josefholmner/Holmner6Axis/3D-models/SolidWorksProject/Axis4_Holder.SLDPRT

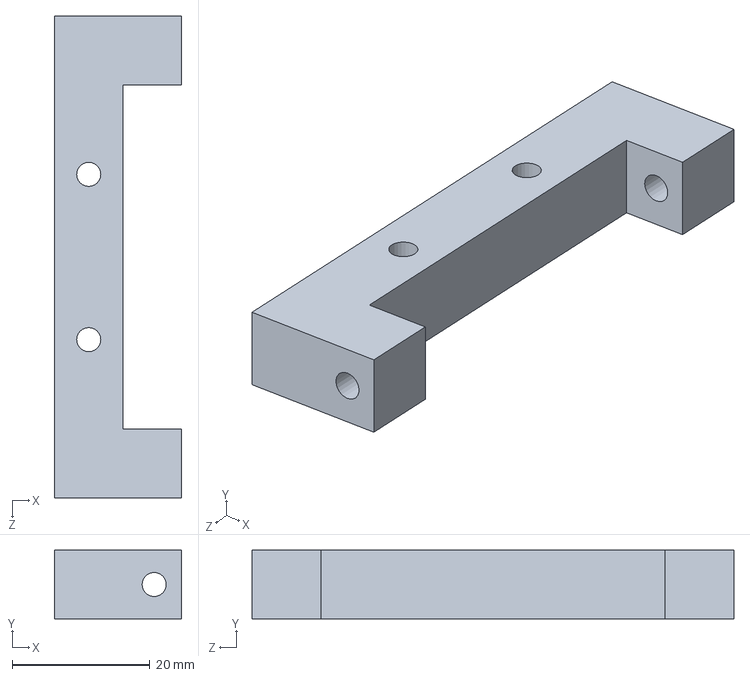
[picture p12: CAD file, 2020-04-25]
3D-models/SolidWorksProject/Axis4_Holder.SLDPRT
18.5 x 10.0 x 70.0 mm
