josefholmner/Holmner6Axis/3D-models/SolidWorksProject/Axis4_Rod.SLDPRT

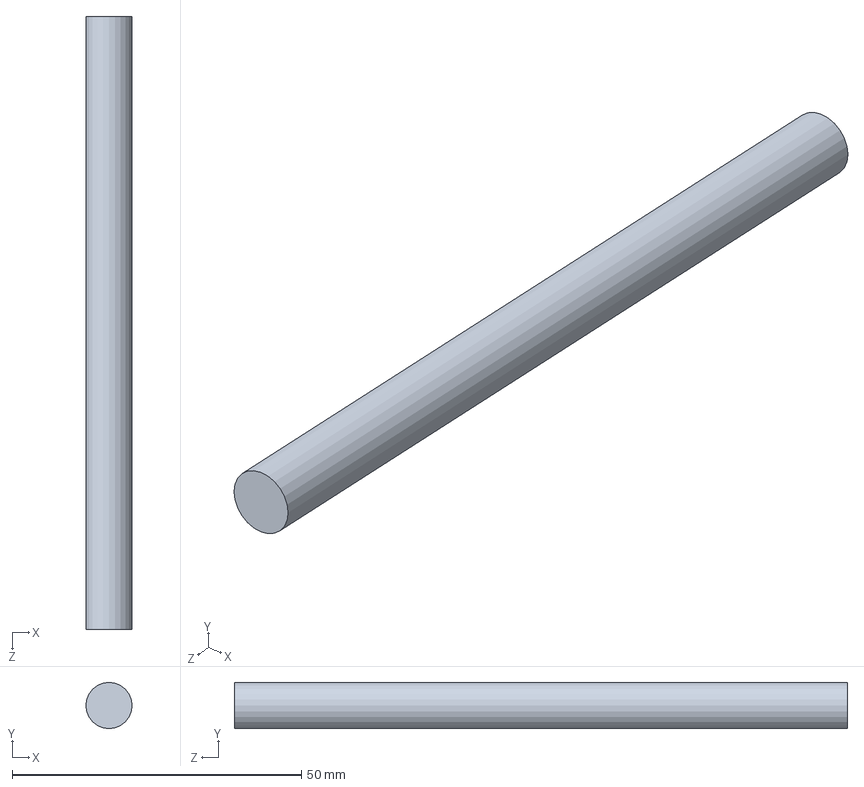
[picture p13: CAD file, 2020-04-25]
3D-models/SolidWorksProject/Axis4_Rod.SLDPRT
8.00 x 8.00 x 106.0 mm
