josefholmner/Holmner6Axis/3D-models/SolidWorksProject/Axis2_Arm_1.SLDPRT

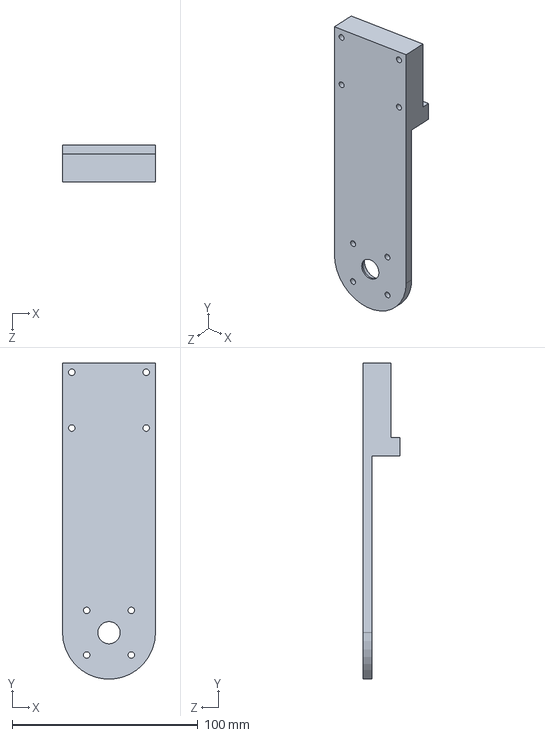
[picture p14: CAD file, 2020-04-25]
3D-models/SolidWorksProject/Axis2_Arm_1.SLDPRT
50.0 x 169.9 x 20.0 mm
