josefholmner/Holmner6Axis/3D-models/SolidWorksProject/Axis5_Cog.SLDPRT

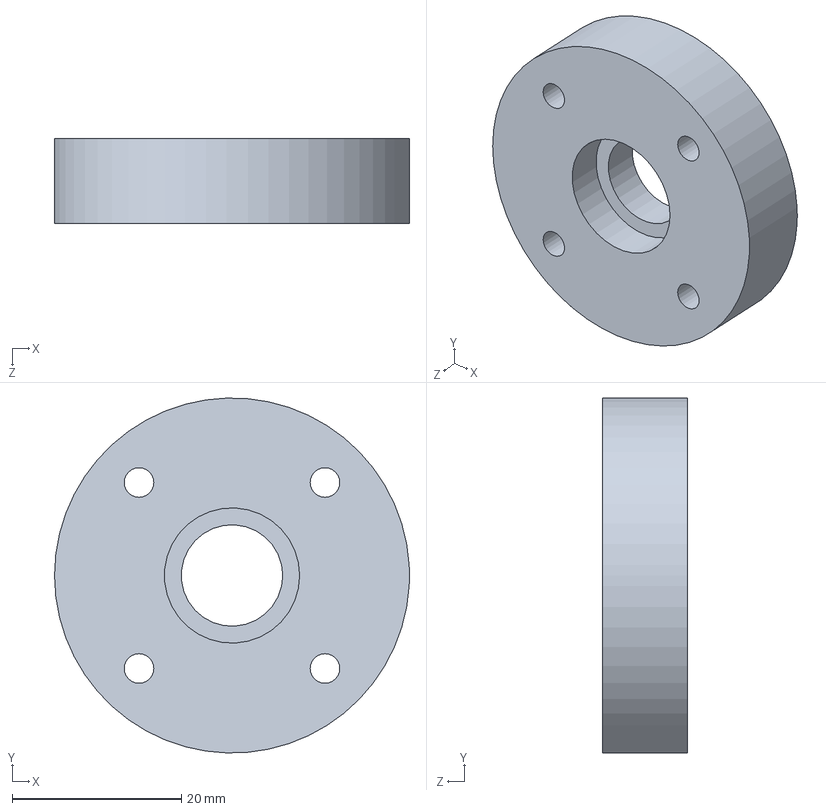
[picture p15: CAD file, 2020-04-25]
3D-models/SolidWorksProject/Axis5_Cog.SLDPRT
42.0 x 42.0 x 10.0 mm
