josefholmner/Holmner6Axis/3D-models/SolidWorksProject/Axis1_Cog.SLDPRT

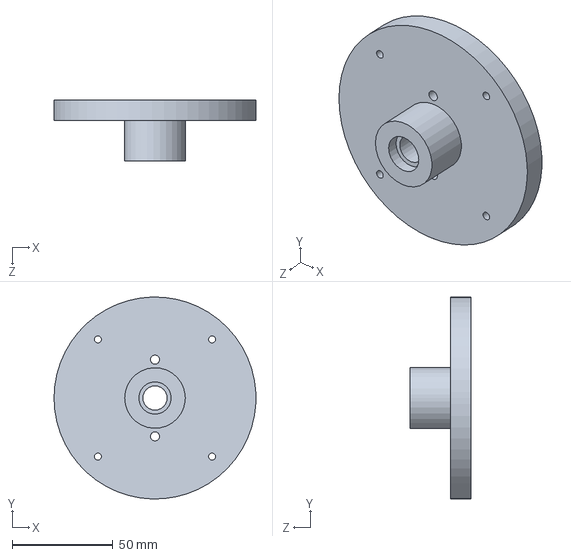
[picture p16: CAD file, 2020-04-25]
3D-models/SolidWorksProject/Axis1_Cog.SLDPRT
100.0 x 100.0 x 30.0 mm
