josefholmner/Holmner6Axis/3D-models/FreeCad/MotorCog_8mm.FCStd

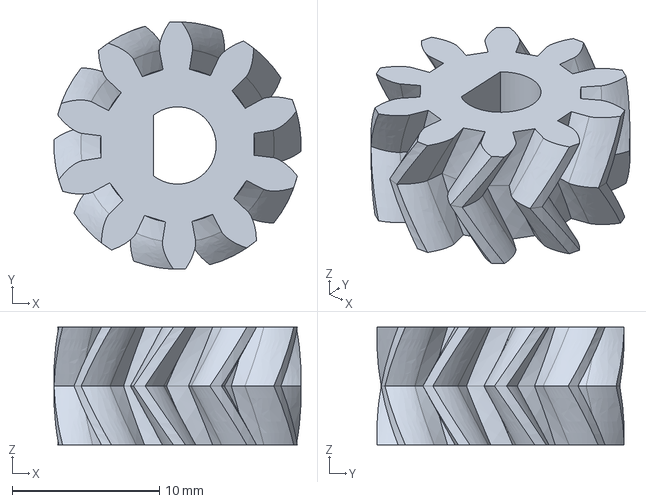
[picture p17: CAD file, 2026-01-18]
3D-models/FreeCad/MotorCog_8mm.FCStd
16.8 x 16.8 x 8.01 mm
