josefholmner/Holmner6Axis/3D-models/SolidWorksProject/Axis5_Rod.SLDPRT

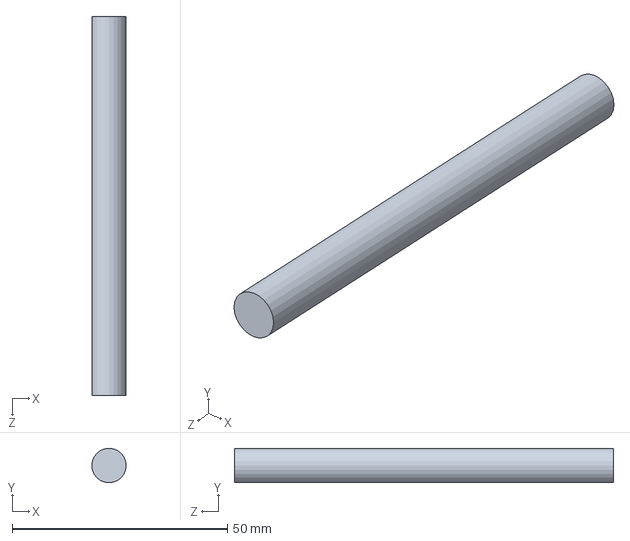
[picture p18: CAD file, 2020-04-25]
3D-models/SolidWorksProject/Axis5_Rod.SLDPRT
8.00 x 8.00 x 88.0 mm
