josefholmner/Holmner6Axis/3D-models/FreeCad/BasePlate.FCStd

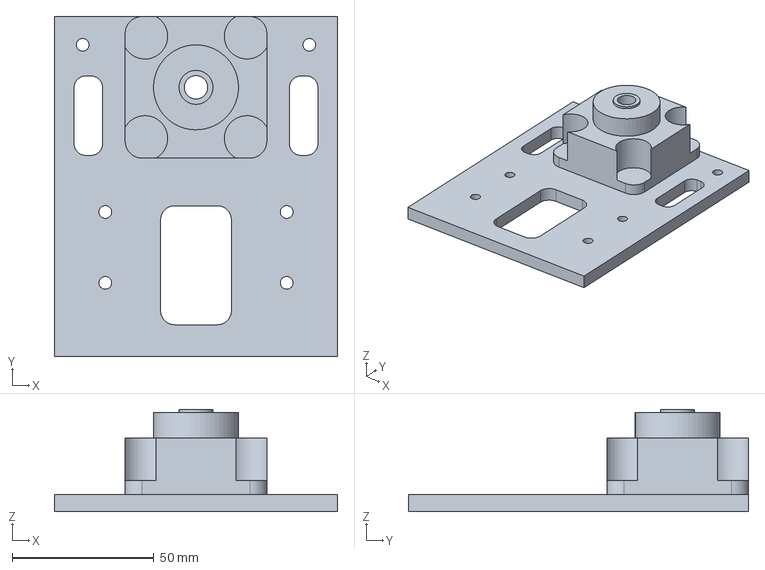
[picture p19: CAD file, 2026-01-17]
3D-models/FreeCad/BasePlate.FCStd
100.0 x 120.0 x 36.0 mm
