josefholmner/Holmner6Axis/3D-models/SolidWorksProject/Axis5_Arm_2_Left.SLDPRT

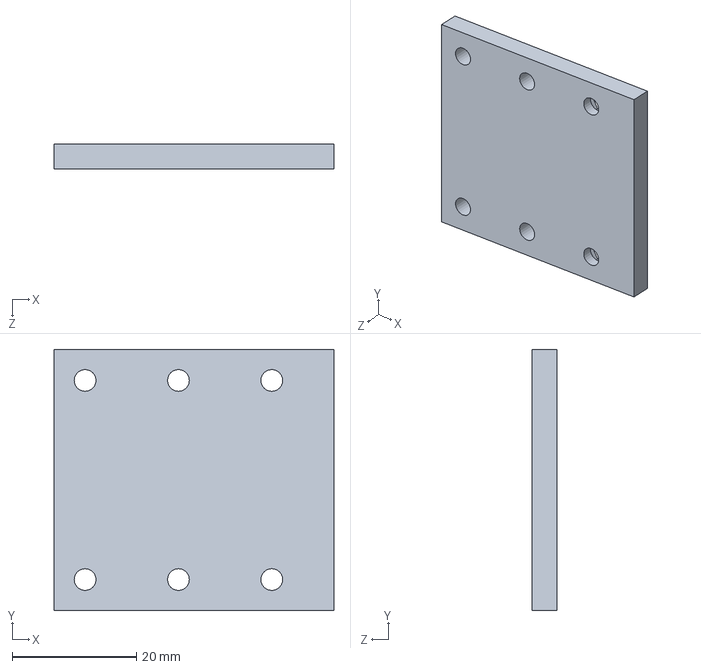
[picture p20: CAD file, 2020-04-25]
3D-models/SolidWorksProject/Axis5_Arm_2_Left.SLDPRT
45.0 x 42.0 x 4.00 mm
