josefholmner/Holmner6Axis/3D-models/SolidWorksProject/Axis2_Holder.SLDPRT

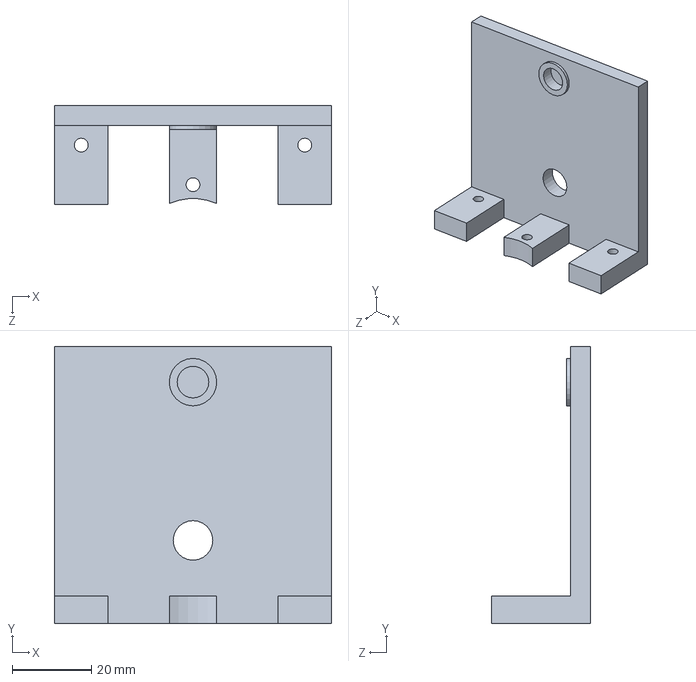
[picture p21: CAD file, 2020-04-25]
3D-models/SolidWorksProject/Axis2_Holder.SLDPRT
70.0 x 70.0 x 25.0 mm
