josefholmner/Holmner6Axis/3D-models/FreeCad/RodStop.FCStd

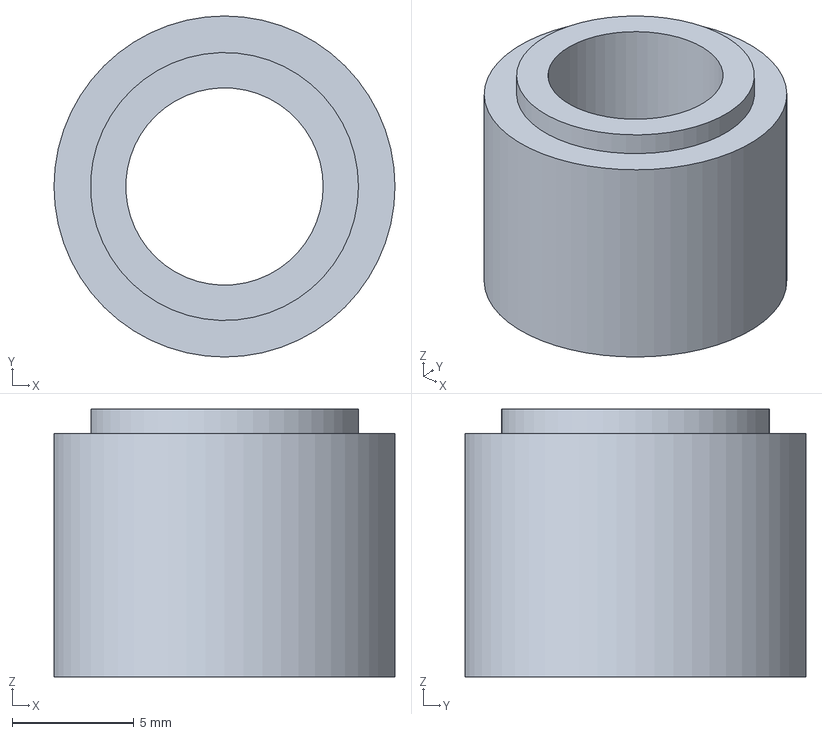
[picture p22: CAD file, 2026-01-13]
3D-models/FreeCad/RodStop.FCStd
14.0 x 14.0 x 11.0 mm
