josefholmner/Holmner6Axis/3D-models/FreeCad/Axis1_RodStop.FCStd

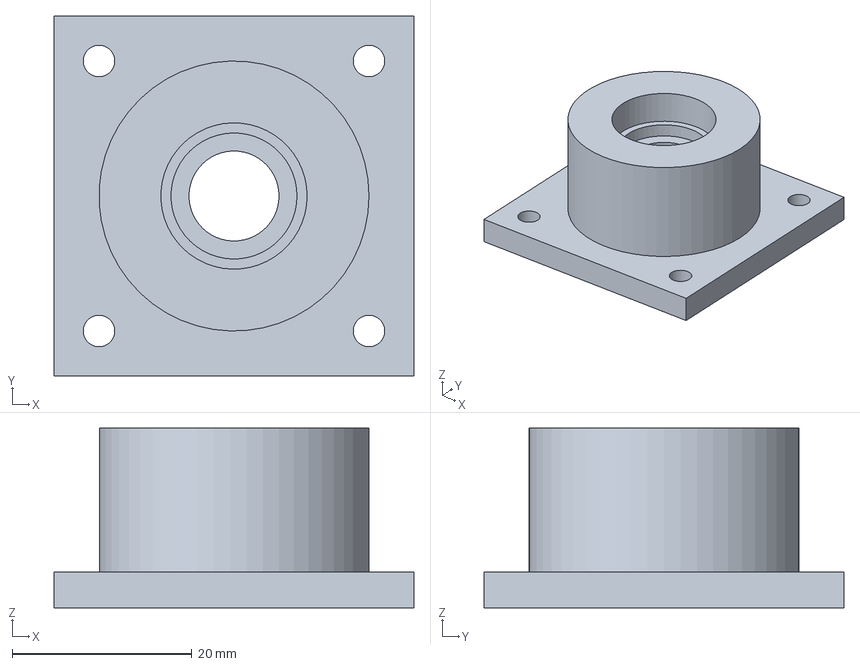
[picture p23: CAD file, 2026-01-13]
3D-models/FreeCad/Axis1_RodStop.FCStd
40.0 x 40.0 x 20.0 mm
