josefholmner/Holmner6Axis/3D-models/SolidWorksProject/Axis2_Rod.SLDPRT

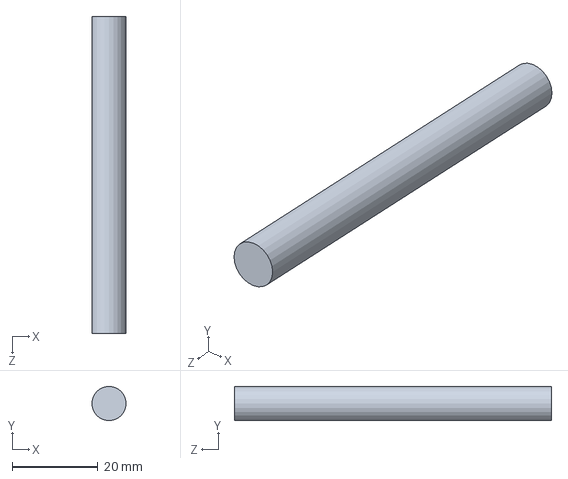
[picture p24: CAD file, 2020-04-25]
3D-models/SolidWorksProject/Axis2_Rod.SLDPRT
8.00 x 8.00 x 74.0 mm
