josefholmner/Holmner6Axis/3D-models/FreeCad/Motor.FCStd

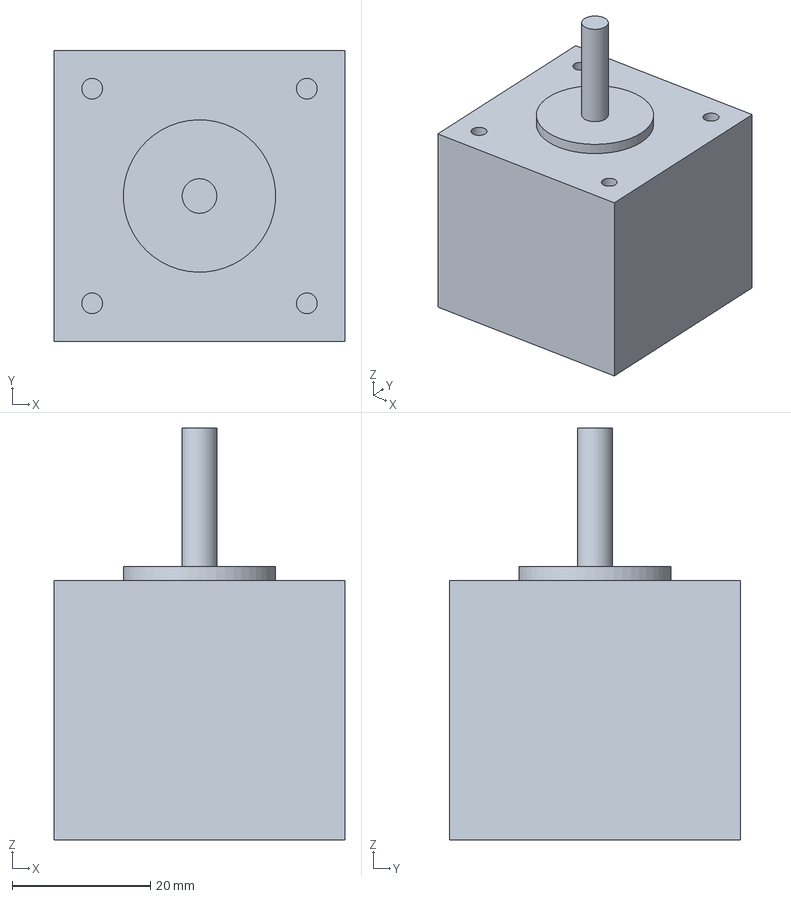
[picture p25: CAD file, 2026-01-09]
3D-models/FreeCad/Motor.FCStd
42.0 x 42.0 x 59.5 mm
