josefholmner/Holmner6Axis/3D-models/SolidWorksProject/Axis0_BottomPlate.SLDPRT

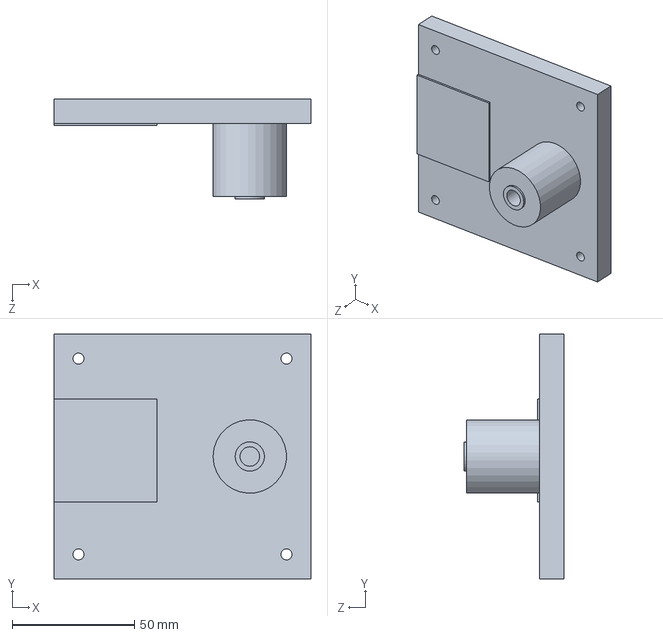
[picture p26: CAD file, 2020-04-25]
3D-models/SolidWorksProject/Axis0_BottomPlate.SLDPRT
105.0 x 100.0 x 41.0 mm
