josefholmner/Holmner6Axis/3D-models/FreeCad/BallBearing.FCStd

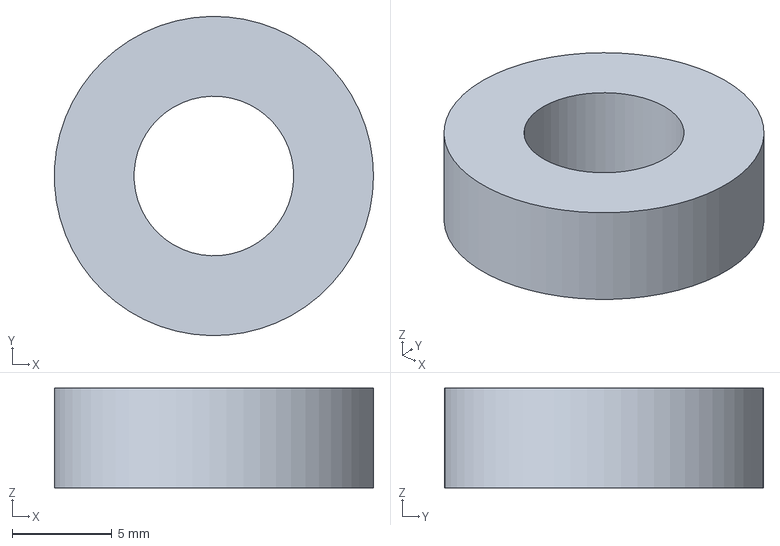
[picture p27: CAD file, 2026-01-09]
3D-models/FreeCad/BallBearing.FCStd
16.0 x 16.0 x 5.00 mm
