josefholmner/Holmner6Axis/3D-models/SolidWorksProject/Axis4_Arm_1_Right.SLDPRT

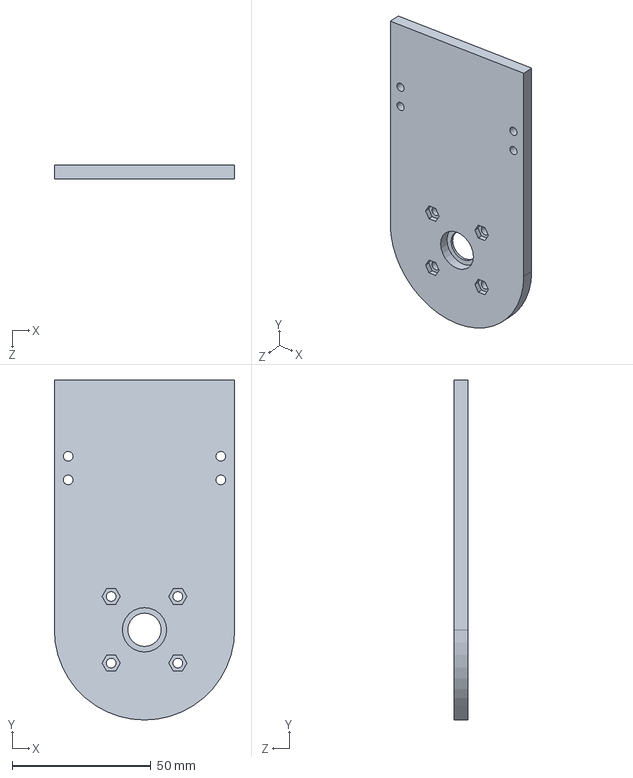
[picture p28: CAD file, 2020-04-25]
3D-models/SolidWorksProject/Axis4_Arm_1_Right.SLDPRT
65.0 x 122.5 x 5.00 mm
