josefholmner/Holmner6Axis/3D-models/SolidWorksProject/Axis2_Arm_2.SLDPRT

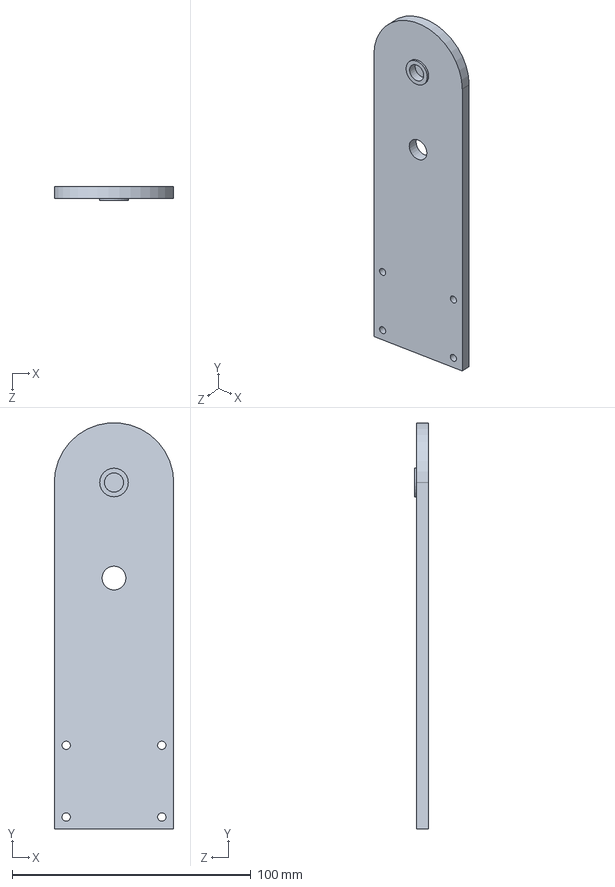
[picture p29: CAD file, 2020-04-25]
3D-models/SolidWorksProject/Axis2_Arm_2.SLDPRT
50.0 x 169.9 x 6.00 mm
