josefholmner/Holmner6Axis/3D-models/SolidWorksProject/Axis4_Arm_1_Left.SLDPRT

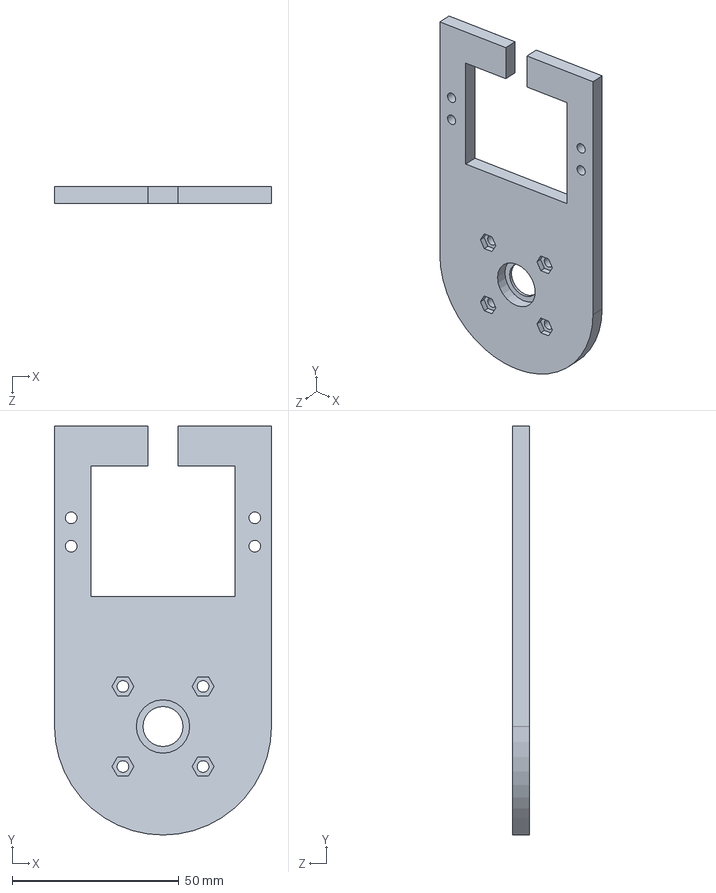
[picture p30: CAD file, 2020-04-25]
3D-models/SolidWorksProject/Axis4_Arm_1_Left.SLDPRT
65.0 x 122.5 x 5.00 mm
