josefholmner/Holmner6Axis/3D-models/SolidWorksProject/Axis5_Arm_Right.SLDPRT

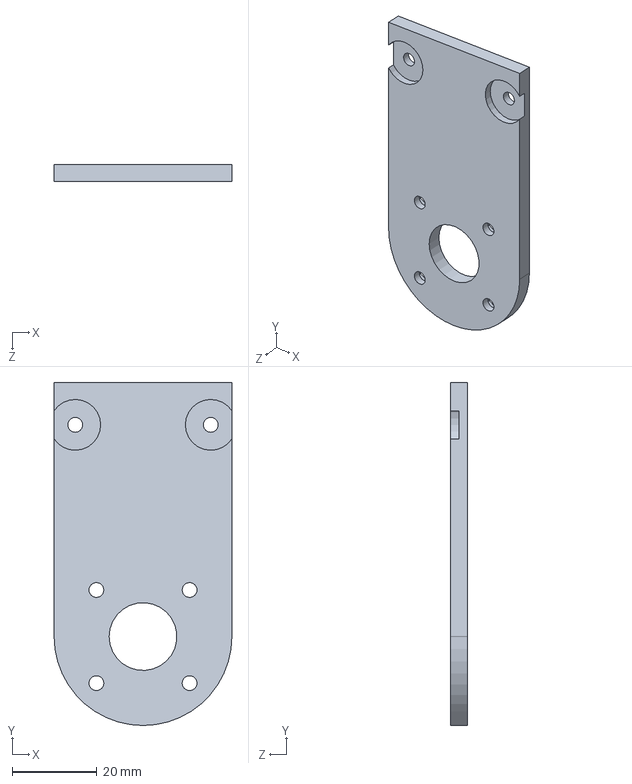
[picture p31: CAD file, 2020-04-25]
3D-models/SolidWorksProject/Axis5_Arm_Right.SLDPRT
42.0 x 81.0 x 4.00 mm
