josefholmner/Holmner6Axis/3D-models/SolidWorksProject/ShaftCoupler.SLDPRT

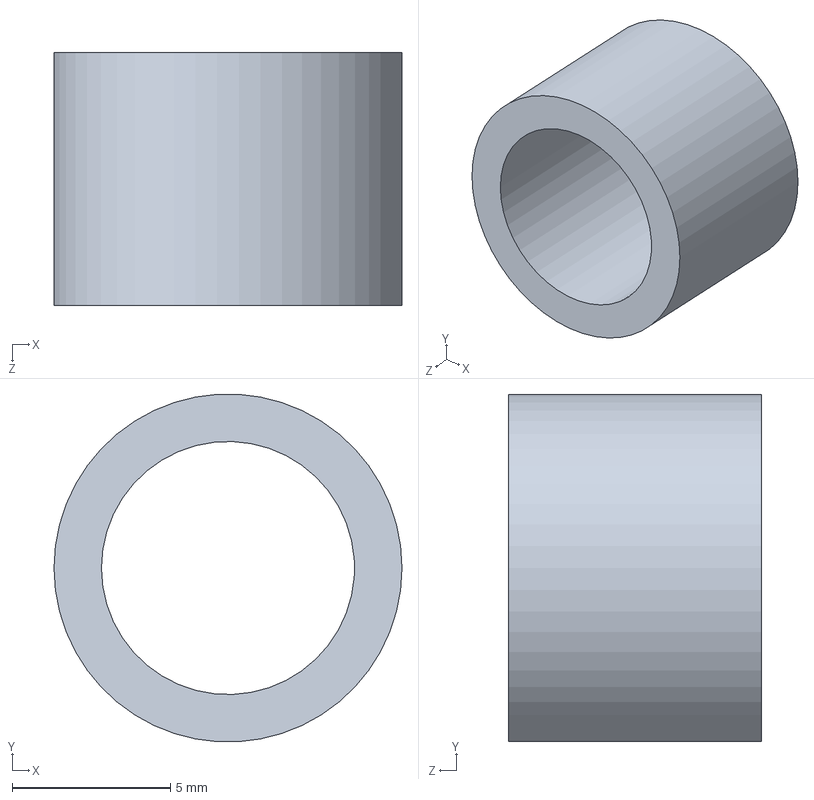
[picture p32: CAD file, 2020-04-25]
3D-models/SolidWorksProject/ShaftCoupler.SLDPRT
11.0 x 11.0 x 8.00 mm
