josefholmner/Holmner6Axis/3D-models/SolidWorksProject/Axis5_Arm_1_Left.SLDPRT

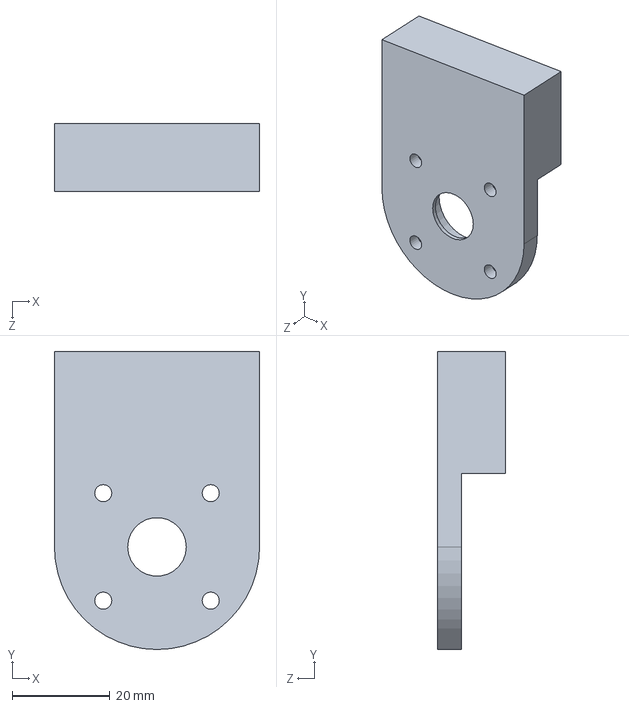
[picture p33: CAD file, 2020-04-25]
3D-models/SolidWorksProject/Axis5_Arm_1_Left.SLDPRT
42.0 x 61.0 x 14.0 mm
