josefholmner/Holmner6Axis/3D-models/SolidWorksProject/Axis3_BearingEnd.SLDPRT

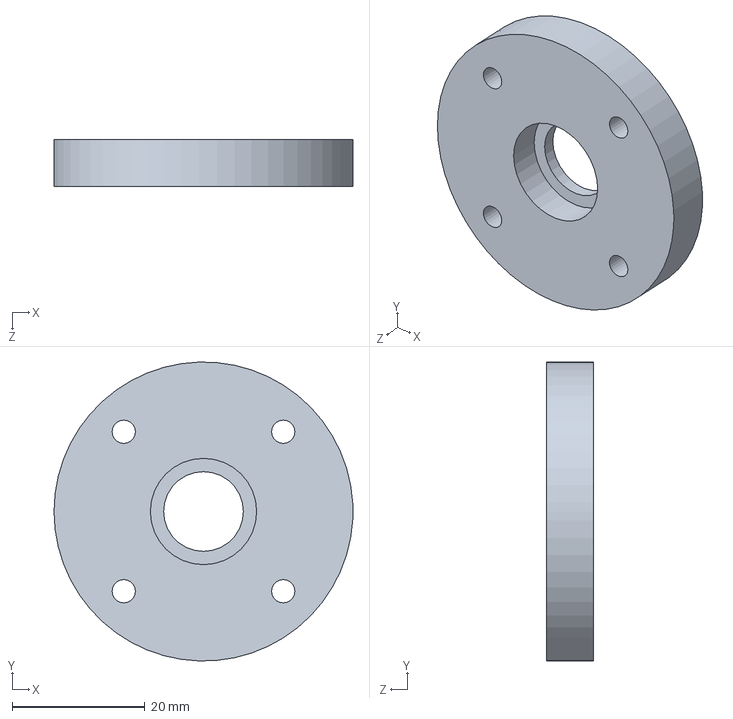
[picture p34: CAD file, 2020-04-25]
3D-models/SolidWorksProject/Axis3_BearingEnd.SLDPRT
45.0 x 45.0 x 7.00 mm
