josefholmner/Holmner6Axis/3D-models/SolidWorksProject/Axis3_Cog.SLDPRT

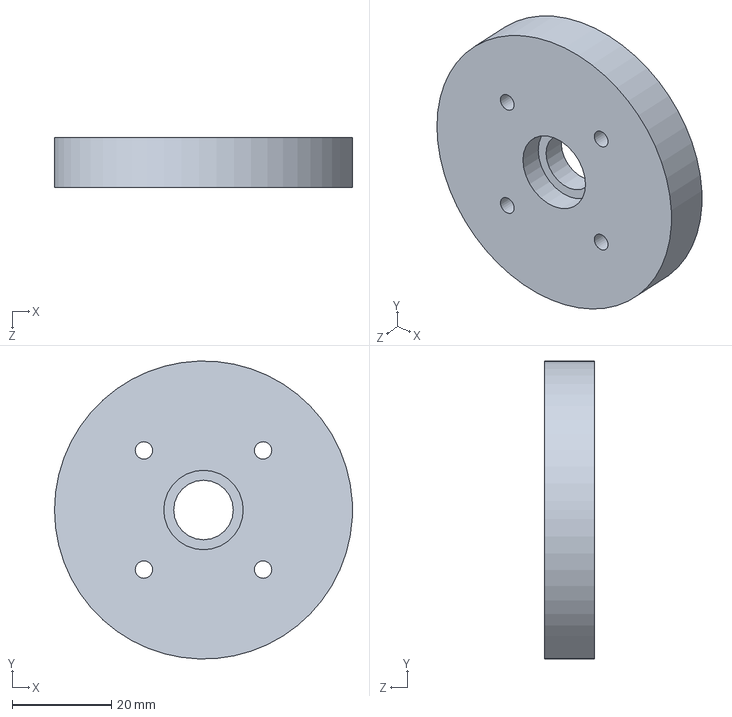
[picture p35: CAD file, 2020-04-25]
3D-models/SolidWorksProject/Axis3_Cog.SLDPRT
60.0 x 60.0 x 10.0 mm
