josefholmner/Holmner6Axis/3D-models/SolidWorksProject/Axis4_RodHolder.SLDPRT

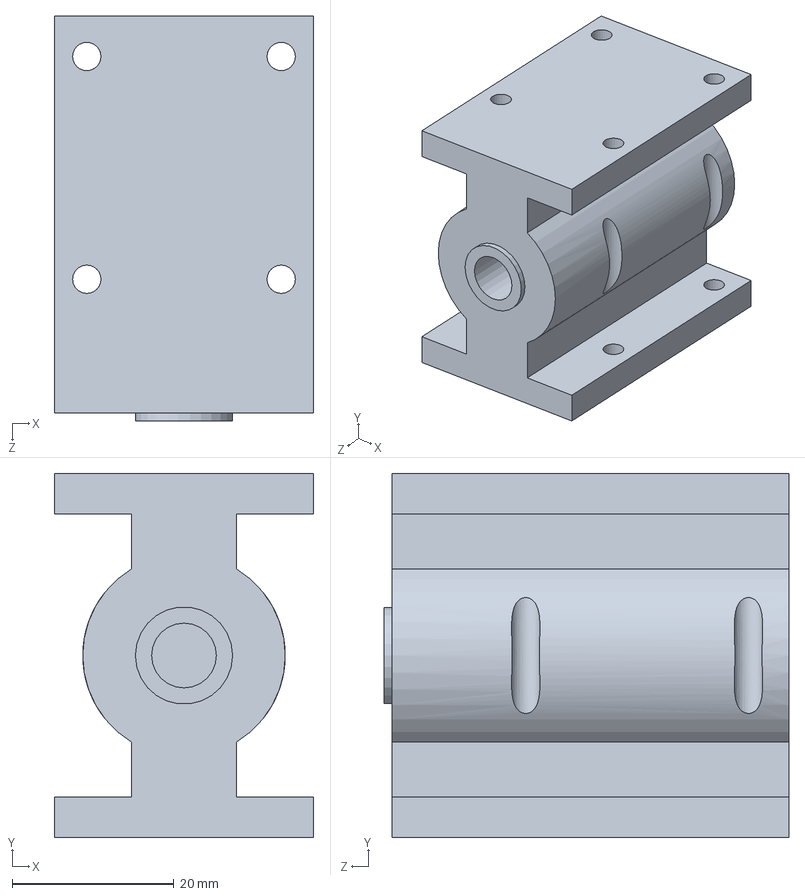
[picture p36: CAD file, 2020-04-25]
3D-models/SolidWorksProject/Axis4_RodHolder.SLDPRT
32.0 x 45.0 x 50.0 mm
