josefholmner/Holmner6Axis/3D-models/SolidWorksProject/StepperMotor.SLDPRT

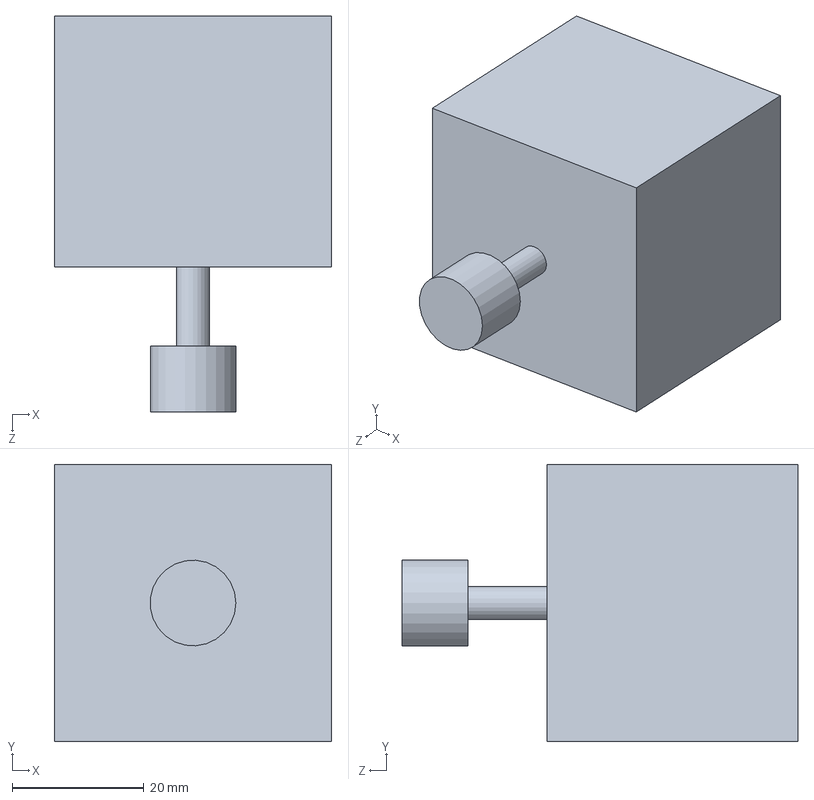
[picture p37: CAD file, 2020-04-25]
3D-models/SolidWorksProject/StepperMotor.SLDPRT
42.0 x 42.0 x 60.0 mm
