josefholmner/Holmner6Axis/3D-models/SolidWorksProject/Axis6_MotorHolder.SLDPRT

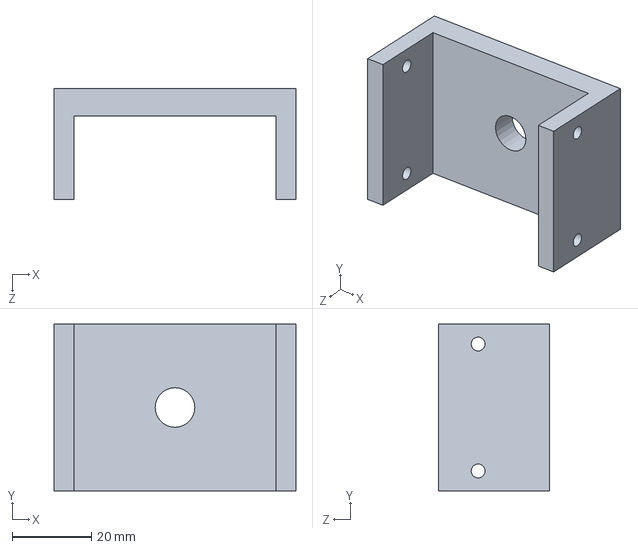
[picture p38: CAD file, 2020-04-25]
3D-models/SolidWorksProject/Axis6_MotorHolder.SLDPRT
61.0 x 42.0 x 28.0 mm
